amd989/Suitchi/src/suitchi/custom_fonts.h

/*
 * custom_fonts.h
 *
 *  Created on: 2020-12-01
 *      Author: amd989 (Alejandro Mora)
 */

// Created by http://oleddisplay.squix.ch/ Consider a donation
// In case of problems make sure that you are using the font file with the correct version!

const uint8_t Moon_Phases_10[] PROGMEM = {
	0x0B, // Width: 11
	0x0A, // Height: 10
	0x20, // First Char: 32
	0xE0, // Numbers of Chars: 224

	// Jump Table:
	0xFF, 0xFF, 0x00, 0x0A,  // 32:65535
	0x00, 0x00, 0x13, 0x0B,  // 33:0
	0x00, 0x13, 0x13, 0x0B,  // 34:19
	0x00, 0x26, 0x13, 0x0B,  // 35:38
	0x00, 0x39, 0x13, 0x0B,  // 36:57
	0x00, 0x4C, 0x13, 0x0B,  // 37:76
	0x00, 0x5F, 0x13, 0x0B,  // 38:95
	0x00, 0x72, 0x13, 0x0B,  // 39:114
	0x00, 0x85, 0x13, 0x0B,  // 40:133
	0x00, 0x98, 0x13, 0x0B,  // 41:152
	0x00, 0xAB, 0x13, 0x0A,  // 42:171
	0x00, 0xBE, 0x11, 0x0A,  // 43:190
	0x00, 0xCF, 0x13, 0x0B,  // 44:207
	0x00, 0xE2, 0x13, 0x0B,  // 45:226
	0x00, 0xF5, 0x13, 0x0B,  // 46:245
	0x01, 0x08, 0x13, 0x0B,  // 47:264
	0x01, 0x1B, 0x13, 0x0A,  // 48:283
	0x01, 0x2E, 0x13, 0x0B,  // 49:302
	0x01, 0x41, 0x13, 0x0B,  // 50:321
	0x01, 0x54, 0x13, 0x0B,  // 51:340
	0x01, 0x67, 0x13, 0x0B,  // 52:359
	0x01, 0x7A, 0x13, 0x0B,  // 53:378
	0x01, 0x8D, 0x13, 0x0B,  // 54:397
	0x01, 0xA0, 0x13, 0x0B,  // 55:416
	0x01, 0xB3, 0x13, 0x0B,  // 56:435
	0x01, 0xC6, 0x13, 0x0B,  // 57:454
	0x01, 0xD9, 0x13, 0x0B,  // 58:473
	0x01, 0xEC, 0x13, 0x0B,  // 59:492
	0x01, 0xFF, 0x13, 0x0B,  // 60:511
	0xFF, 0xFF, 0x00, 0x00,  // 61:65535
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
0xFE, 0x7F, 0x0F, 0xF0, 0x07, 0xE0, 0xF3, 0xCF, 0xF3, 0xCF, 0x07, 0xE0, 0x0F, 0xF0, 0xFF, 0xFF, 0x03, 0xC0, 0x03, 0xC0, 0x1F, 0xFE, 0x7F, 0xF8, 0x03, 0xC0, 0x03, 0xC0, 0xFF, 0xFF, 0xFE, 0x7F, // 51
};
