amd989/Suitchi/src/suitchi/wifi_info.h

/*
 * wifi_info.h
 *
 *  Created on: 2020-12-01
 *      Author: amd989 (Alejandro Mora)
 */

#ifndef WIFI_INFO_H_
#define WIFI_INFO_H_

#if defined(ESP8266)
#include <ESP8266WiFi.h>
#endif
const char *ssid = "";
const char *password = "";

void wifi_connect() {
	WiFi.persistent(false);
	WiFi.mode(WIFI_STA);
	WiFi.setAutoReconnect(true);
	WiFi.begin(ssid, password);
	Serial.println("WiFi connecting...");
	unsigned long start = millis();
	while (!WiFi.isConnected()) {
		if (millis() - start > 30000) {
			Serial.println("\nWiFi connection timeout, restarting...");
			ESP.restart();
		}
		delay(100);
		Serial.print(".");
	}
	Serial.print("\n");
	Serial.printf("WiFi connected, IP: %s\n", WiFi.localIP().toString().c_str());
}

#endif /* WIFI_INFO_H_ */
